rallekralle11/Dact/Dact.png

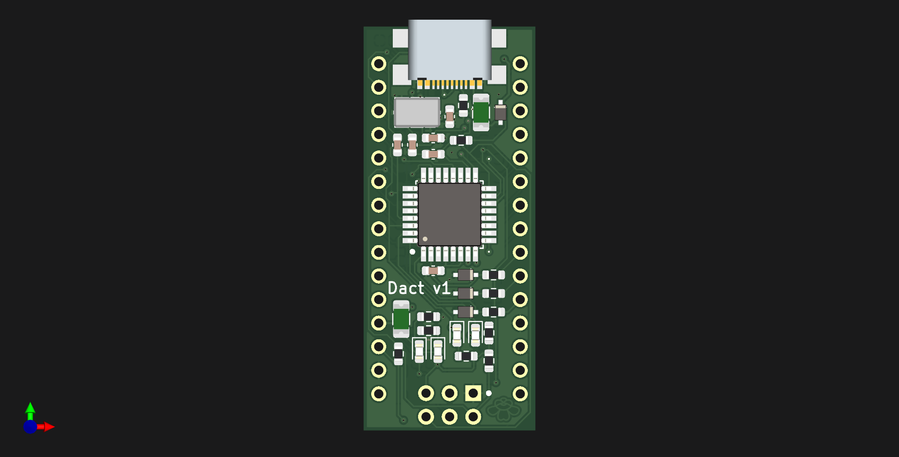
Dact.png
